STEMpedia/evive/softwareFiles/evive/dac_MCP4725.cpp

/**************************************************************************/
/*! 
    @file     Adafruit_MCP4725.cpp
    @author   K.Townsend (Adafruit Industries)
	@license  BSD (see license.txt)
	
	I2C Driver for Microchip's MCP4725 I2C DAC

	This is a library for the Adafruit MCP4725 breakout
	----> http://www.adafruit.com/products/935
		
	Adafruit invests time and resources providing this open source code, 
	please support Adafruit and open-source hardware by purchasing 
	products from Adafruit!

	@section  HISTORY

    v1.0 - First release
	Edited by: Dhrupal R Shah
	http://evive.cc
	Date: 2016/08/01
*/
/**************************************************************************/

#include "dac_MCP4725.h"

/**************************************************************************/
/*! 
    @brief  Instantiates a new MCP4725 class
*/
/**************************************************************************/
dac_MCP4725::dac_MCP4725() {
}

/**************************************************************************/
/*! 
    @brief  Setups the HW
*/
/**************************************************************************/
void dac_MCP4725::begin(uint8_t addr) {
  _i2caddr = addr;
  Wire.begin();

}
 
/**************************************************************************/
/*! 
    @brief  Sets the output voltage to a fraction of source vref.  (Value
            can be 0..4095)

    @param[in]  output
                The 12-bit value representing the relationship between
                the DAC's input voltage and its output voltage.
    @param[in]  writeEEPROM
                If this value is true, 'output' will also be written
                to the MCP4725's internal non-volatile memory, meaning
                that the DAC will retain the current voltage output
                after power-down or reset.
*/
/**************************************************************************/
void dac_MCP4725::setVoltage( uint16_t output, bool writeEEPROM )
{
#ifdef TWBR
  uint8_t twbrback = TWBR;
  // TWBR = ((F_CPU / 400000L) - 16) / 2; // Set I2C frequency to 400kHz
  TWBR = 1;
#endif
  Wire.beginTransmission(_i2caddr);
  if (writeEEPROM)
  {
    Wire.write(MCP4726_CMD_WRITEDACEEPROM);
  }
  else
  {
    Wire.write(MCP4726_CMD_WRITEDAC);
  }
  Wire.write(output / 16);                   // Upper data bits          (D11.D10.D9.D8.D7.D6.D5.D4)
  Wire.write((output % 16) << 4);            // Lower data bits          (D3.D2.D1.D0.x.x.x.x)
  Wire.endTransmission();
#ifdef TWBR
  TWBR = twbrback;
#endif
}

//////////////Modified Library////////////////////
dac_MCP4725 dac;

uint16_t increment = 1, oldIncrement;
float amplitude =  1, oldAmplitude;
int16_t i;
uint16_t lookup = 0;    //varaible for navigating through the tables

//lookup table for Sine Function stored in Flash memory
const PROGMEM uint16_t sineLookUp[1024]= 
{
2048,2061,2073,2086,2098,2111,2123,2136,
2148,2161,2174,2186,2199,2211,2224,2236,
2249,2261,2274,2286,2299,2311,2324,2336,
2349,2361,2373,2386,2398,2411,2423,2435,
2448,2460,2472,2484,2497,2509,2521,2533,
2546,2558,2570,2582,2594,2606,2618,2630,
2643,2655,2667,2678,2690,2702,2714,2726,
2738,2750,2762,2773,2785,2797,2808,2820,
2832,2843,2855,2866,2878,2889,2901,2912,
2924,2935,2946,2958,2969,2980,2991,3002,
3013,3024,3036,3047,3057,3068,3079,3090,
3101,3112,3122,3133,3144,3154,3165,3175,
3186,3196,3207,3217,3227,3238,3248,3258,
3268,3278,3288,3298,3308,3318,3328,3337,
3347,3357,3367,3376,3386,3395,3405,3414,
3423,3433,3442,3451,3460,3469,3478,3487,
3496,3505,3514,3523,3531,3540,3548,3557,
3565,3574,3582,3591,3599,3607,3615,3623,
3631,3639,3647,3655,3663,3670,3678,3685,
3693,3700,3708,3715,3722,3730,3737,3744,
3751,3758,3765,3772,3778,3785,3792,3798,
3805,3811,3817,3824,3830,3836,3842,3848,
3854,3860,3866,3872,3877,3883,3888,3894,
3899,3905,3910,3915,3920,3925,3930,3935,
3940,3945,3950,3954,3959,3963,3968,3972,
3976,3980,3985,3989,3993,3997,4000,4004,
4008,4011,4015,4018,4022,4025,4028,4032,
4035,4038,4041,4043,4046,4049,4052,4054,
4057,4059,4061,4064,4066,4068,4070,4072,
4074,4076,4077,4079,4081,4082,4084,4085,
4086,4087,4088,4089,4090,4091,4092,4093,
4094,4094,4095,4095,4095,4095,4095,4095,
4095,4095,4095,4095,4095,4095,4095,4094,
4094,4093,4092,4091,4090,4089,4088,4087,
4086,4085,4084,4082,4081,4079,4077,4076,
4074,4072,4070,4068,4066,4064,4061,4059,
4057,4054,4052,4049,4046,4043,4041,4038,
4035,4032,4028,4025,4022,4018,4015,4011,
4008,4004,4000,3997,3993,3989,3985,3980,
3976,3972,3968,3963,3959,3954,3950,3945,
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
};

void setFrequencyAmplitude(){
  //Set the Frequency and Amplitude
  oldIncrement = increment;
  oldAmplitude = amplitude;
  increment = (analogRead(POT1)>>4)+1;
  amplitude = ((analogRead(POT2)>>4)/64.0);
}

//Function to output one wave complete sine wave form
void generateSineWave(){
  for (i = 0; i < 1024; i= i + increment)
  {
    dac.setVoltage(pgm_read_word(&(sineLookUp[i]))*amplitude, false);
  }
}

//Function to output one wave complete sqaure wave form
void generateSquareWave(){
  for (i = 0; i < 512; i= i + increment)
  {
    dac.setVoltage(amplitude*4095, false);
  }
  for (i = 512; i > 0; i= i - increment)
  {
    dac.setVoltage(0, false);
  } 
}

//Function to output one wave complete triangular wave form
void generateTraingularWave(){
  for (i = 0; i < 512; i= i + increment)
  {
    dac.setVoltage(i*8*amplitude, false);
  }
  for (i = 512; i > 0; i= i - increment)
  {
    dac.setVoltage(i*8*amplitude, false);
  }  
}

//Function to output one wave complete sawtooth wave (up) form
void generateSawtoothWaveUp(){
  for (i = 0; i < 1024; i= i + increment)
  {
    dac.setVoltage(i*4*amplitude, false);
  }
}

//Function to output one wave complete sawtooth wave (down) form
void generateSawtoothWaveDown(){
  for (i = 1023; i > 0; i= i - increment)
  {
    dac.setVoltage(i*4*amplitude, false);
  }
}

//Function to output one wave complete sqaure wave form
void generateAnalogOutput(){
  dac.setVoltage(4095*amplitude, false);
}
