STEMpedia/evive/testCodes/testUserDefinedFunctions/evivePins.h

#ifndef EVIVEPINS_H
#define EVIVEPINS_H

#define LCD_RST  			47
#define LCD_CS  			48
#define LCD_DC   			49
#define SPI_MISO 			50
#define SPI_MOSI 			51
#define SPI_SCK 			52
#define SD_CS 				34
#define ADC_CS 				35 
#define ADC_DREADY 			32
#define MOTOR1_D1 			28
#define MOTOR1_D2 			29
#define MOTOR1_EN 			44			// PWM
#define MOTOR2_D1 			30
#define MOTOR2_D2 			31
#define MOTOR2_EN 			45			// PWM
#define STEPPER_D1			28
#define STEPPER_D2			29
#define STEPPER_D3			30
#define STEPPER_D4			31
#define SERVO1_ATTACH 		44
#define SERVO2_ATTACH 		45
#define TACTILESW1 			38
#define TACTILESW2 			39
#define SLIDESW1_D1		 	40
#define SLIDESW1_D2 		41
#define SLIDESW2_D1 		42
#define SLIDESW2_D2 		43
#define POT1	 			A9
#define POT2 				A10
#define LEVELSHIFTER_DIR	33
#define VINSUPPLYLEVEL	 	A6
#define VARSUPPLYLEVEL	 	A7
#define BATSUPPLYLEVEL 		A8
#define NAVKEY_MOVE			A11
#define NAVKEY_PRESS		19
#define LED13				13
#define TIMER				46
#define BUZZER				46
#define IO3V3_PIN1 			36
#define IO3V3_PIN2 			37

#endif
