STEMpedia/evive/testCodes/testMotors/testMotors.ino

void setup(){
  /*pinMode(A9, INPUT);
  pinMode(44,OUTPUT);
  pinMode(28,OUTPUT);
  pinMode(29,OUTPUT);
  pinMode(40,INPUT);
  pinMode(41,INPUT);
   pinMode(30,OUTPUT);
  digitalWrite(28,LOW);
  digitalWrite(29,HIGH);
  digitalWrite(30,LOW);
  analogWrite(44,255);

  pinMode(A10, INPUT);
  pinMode(45,OUTPUT);
  pinMode(30,OUTPUT);
  pinMode(31,OUTPUT);
  pinMode(42,INPUT);
  pinMode(43,INPUT);
  digitalWrite(30,LOW);
  digitalWrite(31,HIGH);
  analogWrite(45,255);*/
pinMode(28,OUTPUT);
pinMode(30,OUTPUT);
digitalWrite(28,HIGH);
digitalWrite(30,LOW);
}
void loop(){
//  digitalWrite(28,digitalRead(40));
//  digitalWrite(29,digitalRead(41));
//  digitalWrite(30,digitalRead(42));
//  digitalWrite(31,digitalRead(43));
  //analogWrite(44, analogRead(A9)/4);
//    digitalWrite(28,digitalRead(40));
//  digitalWrite(29,digitalRead(41));
//digitalWrite(28,HIGH);
//digitalWrite(30,LOW);

digitalWrite(30,LOW);
digitalWrite(28,HIGH);


}
