STEMpedia/evive/testCodes/testUserDefinedFunctions/bitmaps.h

#ifndef BITMAPS_H
#define BITMAPS_H

//Bell icon size: 16W*16H
const unsigned char bell [] PROGMEM = {
0x01, 0x80, 0x03, 0xc0, 0x0f, 0xf0, 0x1f, 0xf8, 0x1f, 0xf8, 0x1f, 0xf8, 0x3f, 0xfc, 0x3f, 0xfc, 
0x3f, 0xfc, 0x3f, 0xfc, 0x3f, 0xfc, 0x7f, 0xfe, 0x7f, 0xfe, 0xc3, 0xc3, 0xc3, 0xc3, 0x3f, 0xfc, 
};

//SemiCircle size: 50W*25H
const unsigned char semiCircle [] PROGMEM = {
0x00, 0x00, 0x0f, 0xfc, 0x00, 0x00, 0x00, 
0x00, 0x00, 0x7f, 0xff, 0x80, 0x00, 0x00, 
0x00, 0x03, 0xff, 0xff, 0xf0, 0x00, 0x00, 
0x00, 0x0f, 0xf0, 0x03, 0xfc, 0x00, 0x00, 
0x00, 0x1f, 0x80, 0x00, 0x7e, 0x00, 0x00, 
0x00, 0x7e, 0x00, 0x00, 0x1f, 0x80, 0x00, 
0x00, 0xf8, 0x00, 0x00, 0x07, 0xc0, 0x00, 
0x01, 0xf0, 0x00, 0x00, 0x03, 0xe0, 0x00, 
0x03, 0xc0, 0x00, 0x00, 0x00, 0xf0, 0x00, 
0x07, 0x80, 0x00, 0x00, 0x00, 0x78, 0x00, 
0x07, 0x00, 0x00, 0x00, 0x00, 0x38, 0x00, 
0x0f, 0x00, 0x00, 0x00, 0x00, 0x3c, 0x00, 
0x1e, 0x00, 0x00, 0x00, 0x00, 0x1e, 0x00, 
0x1c, 0x00, 0x00, 0x00, 0x00, 0x0e, 0x00, 
0x3c, 0x00, 0x00, 0x00, 0x00, 0x0f, 0x00, 
0x38, 0x00, 0x00, 0x00, 0x00, 0x07, 0x00, 
0x38, 0x00, 0x00, 0x00, 0x00, 0x07, 0x80, 
0x70, 0x00, 0x00, 0x00, 0x00, 0x03, 0x80, 
0x70, 0x00, 0x00, 0x00, 0x00, 0x03, 0x80, 
0x70, 0x00, 0x00, 0x00, 0x00, 0x03, 0x80, 
0xe0, 0x00, 0x00, 0x00, 0x00, 0x01, 0xc0, 
0xe0, 0x00, 0x00, 0x00, 0x00, 0x01, 0xc0, 
0xe0, 0x00, 0x00, 0x00, 0x00, 0x01, 0xc0, 
0xe0, 0x00, 0x00, 0x00, 0x00, 0x01, 0xc0, 
0xe0, 0x00, 0x00, 0x00, 0x00, 0x01, 0xc0
};

//evive_logo Size: 71W*71H
const unsigned char evive_logo [] PROGMEM = {
0x00, 0x00, 0x00, 0x00, 0x00, 0x00, 0x00, 0x00, 0x00, 
0x00, 0x00, 0x00, 0x00, 0xfc, 0x00, 0x00, 0x00, 0x00, 
0x00, 0x00, 0x00, 0x1f, 0xff, 0xf0, 0x00, 0x00, 0x00, 
0x00, 0x00, 0x01, 0xff, 0xff, 0xfe, 0x00, 0x00, 0x00, 
0x00, 0x00, 0x07, 0xff, 0xff, 0xff, 0xc0, 0x00, 0x00, 
0x00, 0x00, 0x1f, 0xff, 0xff, 0xff, 0xf0, 0x00, 0x00, 
0x00, 0x00, 0x7f, 0xff, 0xff, 0xff, 0xf8, 0x00, 0x00, 
0x00, 0x00, 0xff, 0xff, 0xff, 0xff, 0xfe, 0x00, 0x00, 
0x00, 0x03, 0xff, 0xfc, 0x00, 0x7f, 0xff, 0x00, 0x00, 
0x00, 0x07, 0xff, 0xc0, 0x00, 0x07, 0xff, 0xc0, 0x00, 
0x00, 0x0f, 0xff, 0x00, 0x00, 0x01, 0xff, 0xc0, 0x00, 
0x00, 0x0f, 0xfc, 0x00, 0x00, 0x00, 0x7f, 0xe0, 0x00, 
0x00, 0x07, 0xf8, 0x07, 0xff, 0x80, 0x3f, 0xc0, 0x00, 
0x00, 0x03, 0xf8, 0x1f, 0xff, 0xf0, 0x0f, 0x80, 0x00, 
0x00, 0x01, 0xfc, 0x7f, 0xff, 0xfc, 0x07, 0x00, 0x00, 
0x00, 0x00, 0xff, 0xff, 0xff, 0xff, 0x00, 0x00, 0x00, 
0x00, 0x00, 0x7f, 0xff, 0xff, 0xff, 0x80, 0x00, 0x00, 
0x00, 0x00, 0x3f, 0xfc, 0x00, 0x7f, 0xc0, 0x00, 0x00, 
0x00, 0x00, 0x1f, 0xe0, 0x00, 0x1f, 0xe0, 0x00, 0x00, 
0x02, 0x00, 0x0f, 0xc0, 0x00, 0x07, 0xe0, 0x00, 0x80, 
0x07, 0x80, 0x07, 0xc0, 0x00, 0x01, 0xc0, 0x03, 0xc0, 
0x0f, 0xc0, 0x03, 0xe3, 0xff, 0x80, 0x00, 0x0f, 0xe0, 
0x0f, 0xf0, 0x01, 0xff, 0xff, 0xe0, 0x00, 0x1f, 0xe0, 
0x1f, 0xfc, 0x00, 0xff, 0xff, 0xf0, 0x00, 0x7f, 0xe0, 
0x1f, 0xff, 0x00, 0x7f, 0xff, 0xf8, 0x01, 0xff, 0xf0, 
0x1f, 0xff, 0x80, 0x3f, 0x83, 0xf8, 0x07, 0xff, 0xe0, 
0x07, 0xff, 0xe0, 0x1e, 0x00, 0xf0, 0x0f, 0xff, 0xc0, 
0x03, 0xff, 0xf8, 0x08, 0x00, 0x00, 0x3f, 0xff, 0x00, 
0x00, 0xff, 0xfe, 0x00, 0x00, 0x00, 0xff, 0xfc, 0x00, 
0x00, 0x3f, 0xff, 0x00, 0x00, 0x01, 0xff, 0xf8, 0x00, 
0x00, 0x0f, 0xff, 0xc0, 0xfe, 0x07, 0xff, 0xe0, 0x00, 
0x00, 0x07, 0xff, 0xc1, 0xff, 0x07, 0xff, 0x80, 0x00, 
0x00, 0x01, 0xff, 0xc3, 0xff, 0x87, 0xff, 0x00, 0x00, 
0x00, 0x00, 0x7f, 0x83, 0xff, 0x87, 0xfc, 0x00, 0x00, 
0x00, 0x00, 0x3f, 0x83, 0xff, 0x83, 0xf8, 0x00, 0x00, 
0x00, 0x00, 0x3f, 0x83, 0xff, 0x83, 0xf8, 0x00, 0x00, 
0x00, 0x00, 0x3f, 0x83, 0xff, 0x83, 0xf8, 0x00, 0x00, 
0x00, 0x00, 0x7f, 0x83, 0xff, 0x87, 0xfc, 0x00, 0x00, 
0x00, 0x01, 0xff, 0xc3, 0xff, 0x87, 0xfe, 0x00, 0x00, 
0x00, 0x03, 0xff, 0xc1, 0xff, 0x07, 0xff, 0x80, 0x00, 
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
};
#endif
